romainflcht/lightlink/embedded_program/vibration_motor.h

#ifndef VIBRATION_MOTOR_H
#define VIBRATION_MOTOR_H

#include "configuration.h"
#include <Arduino.h>

// CONSTANTS : 
#define VIBRATION_MOTOR_PIN 33

// FUNCTIONS : 
void vibrate(); 
void haptic(); 

#endif
