romainflcht/lightlink/embedded_program/tft_bitmap.h

#define DEFAULT_ICON_SIZE  16
#define WARNING_ICON_SIZE  4
#define QRCODE_ICON_SIZE   25
#define QRCODE_PIXEL_SIZE  5


// WIFI_ICON [sym] (8x16).
const uint8_t WIFI_ICON[] PROGMEM = {
  0x00, 0xf0, 0xfc, 0x1f, 0x03, 0xe1, 0xf8, 0x1c, 0x0c, 0xc0, 0xf0, 0x30, 0x00, 0x80, 0x80, 0x00
};

// ERROR_ICON [sym] (8x16).
const uint8_t ERROR_ICON[] PROGMEM = {
  0x07, 0x0f, 0x1f, 0x3e, 0x7c, 0xf8, 0xf0, 0xe0, 0xe0, 0xf0, 0xf8, 0x7c, 0x3e, 0x1f, 0x0f, 0x07
};

// WARNING_ICON (2x16).
const uint8_t WARNING_ICON[] PROGMEM = {
  0x00, 0x80, 0xc0, 0xc0, 0xc0, 0xc0, 0xc0, 0xc0, 0xc0, 0x80, 0x00, 0x80, 0xc0, 0xc0, 0x80, 0x00
};

// BATTERY_ICON [sym] (8x16).
const uint8_t BATTERY_ICON[] PROGMEM = {
  0xc0, 0xc0, 0xf0, 0xf8, 0x18, 0x18, 0x18, 0x18, 0x18, 0x18, 0x18, 0x18, 0x18, 0x18, 0xf8, 0xf0
};

// BATTERY_CHARGE_ICON (16x16).
const uint8_t BATTERY_CHARGE_ICON[] PROGMEM = {
  0x00, 0x1e, 0x00, 0x1f, 0x80, 0x0f, 0x80, 0x07, 0xc0, 0x03, 0xe0, 0x01, 0xf0, 0x01, 0xf8, 0x3f,
  0xfc, 0x3f, 0xfc, 0x1f, 0xf8, 0x1f, 0x80, 0x0f, 0x80, 0x07, 0xc0, 0x03, 0xe0, 0x01, 0xf0, 0x00
};

const unsigned char QRCODE[] PROGMEM = {
	0x01, 0xbd, 0xc0, 0x00, 0x7d, 0x23, 0xdf, 0x00, 0x45, 0x8b, 0x51, 0x00, 0x45, 0x20, 0xd1, 0x00, 
	0x45, 0xd7, 0x51, 0x00, 0x7d, 0x51, 0xdf, 0x00, 0x01, 0x55, 0x40, 0x00, 0xff, 0xf7, 0x7f, 0x80, 
	0x04, 0x1c, 0x2a, 0x80, 0xde, 0x2e, 0xc7, 0x00, 0x5c, 0x21, 0x95, 0x80, 0x13, 0x87, 0x6f, 0x80, 
	0x21, 0xb4, 0xe2, 0x00, 0x23, 0x1e, 0x07, 0x80, 0x59, 0x19, 0x95, 0x80, 0x7a, 0xcb, 0x7e, 0x00, 
	0x49, 0x78, 0x03, 0x00, 0xff, 0x3e, 0x77, 0x00, 0x01, 0x10, 0x54, 0x00, 0x7d, 0xcd, 0x73, 0x80, 
	0x45, 0x12, 0x03, 0x80, 0x45, 0x0d, 0x02, 0x00, 0x45, 0x23, 0xa5, 0x00, 0x7d, 0x6a, 0x90, 0x80, 
	0x01, 0x70, 0x78, 0x00
};
